phobos-/PhobosLT/stl/IMG_20241015_093013.jpg

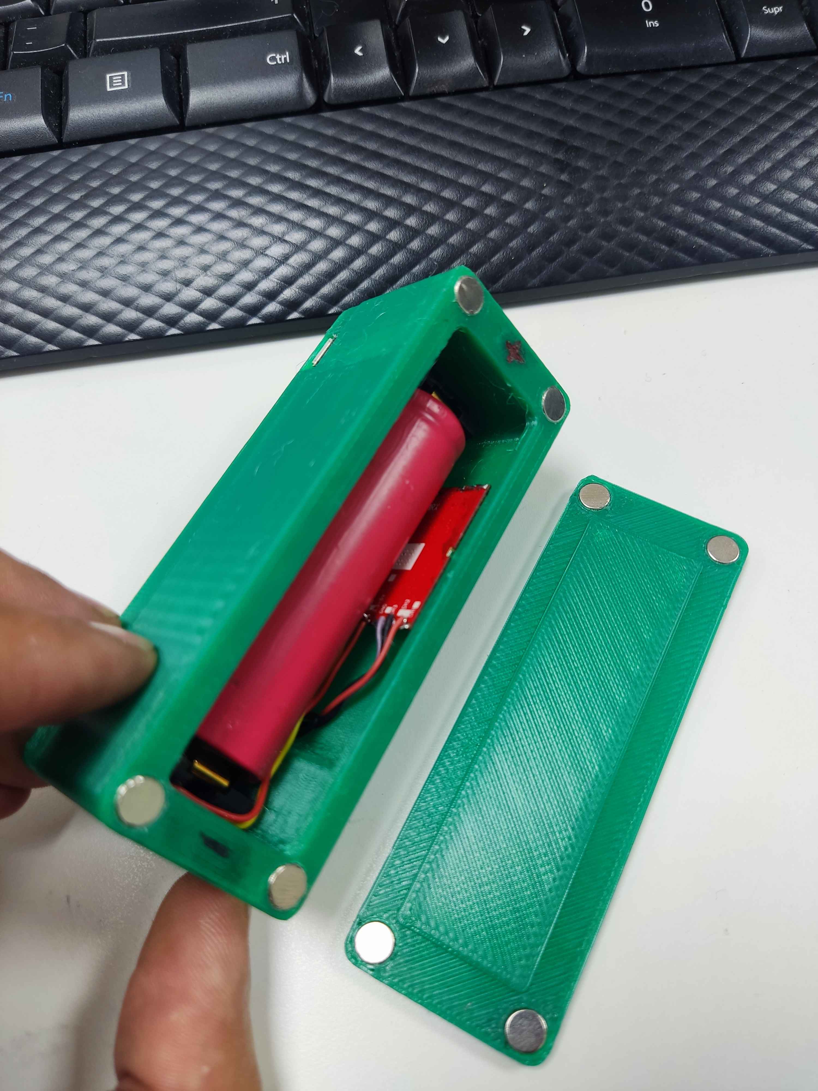
stl/IMG_20241015_093013.jpg
